brickbots/pimech_deck/case/screen_tray_top_v01.stl

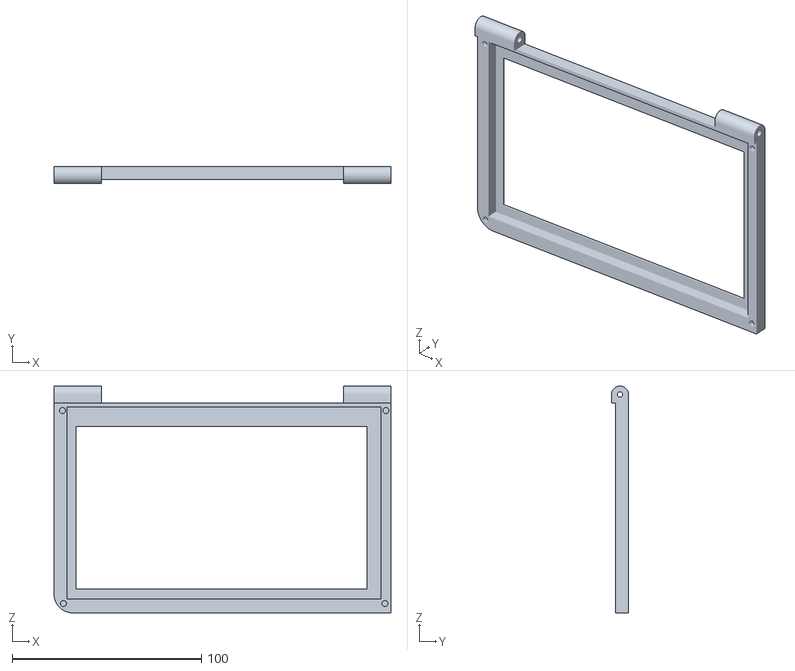
[picture p27: CAD file, 2021-03-30]
case/screen_tray_top_v01.stl
178.2 x 9.00 x 120.0
